Open-Smartwatch/3d-files/case-gps-0.8mm-pcb-20mm-straps/case-gps-top.stl

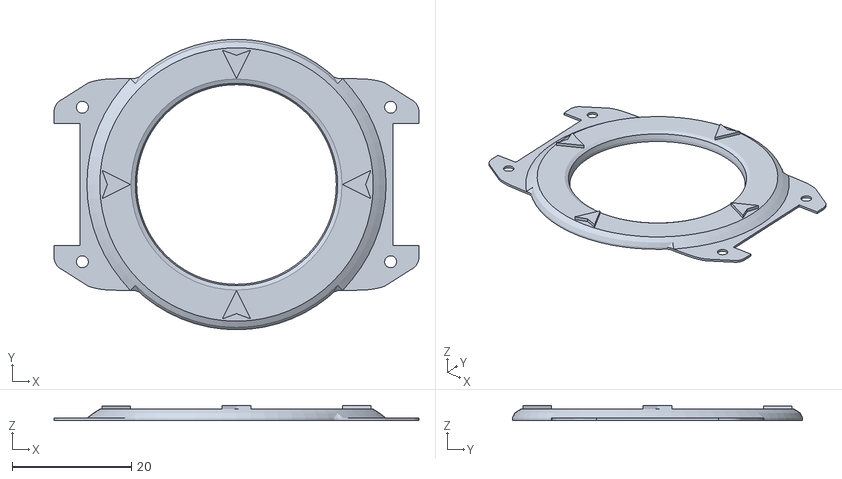
[picture p14: CAD file, 2021-03-20]
case-gps-0.8mm-pcb-20mm-straps/case-gps-top.stl
61.1 x 48.6 x 2.50
