Open-Smartwatch/3d-files/case-light-0.8mm-pcb-20mm-straps/case-light-0.8mm-pcb-20mm-straps-2-pla.stl

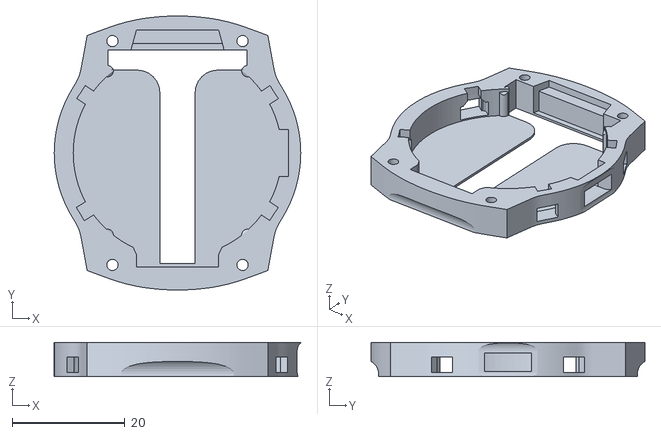
[picture p15: CAD file, 2021-04-03]
case-light-0.8mm-pcb-20mm-straps/case-light-0.8mm-pcb-20mm-straps-2-pla.stl
43.7 x 48.6 x 6.10
