Open-Smartwatch/3d-files/case-light-1.6mm-pcb-20mm-straps/case-light-1.6mm-pcb-20mm-straps-2-pla.stl

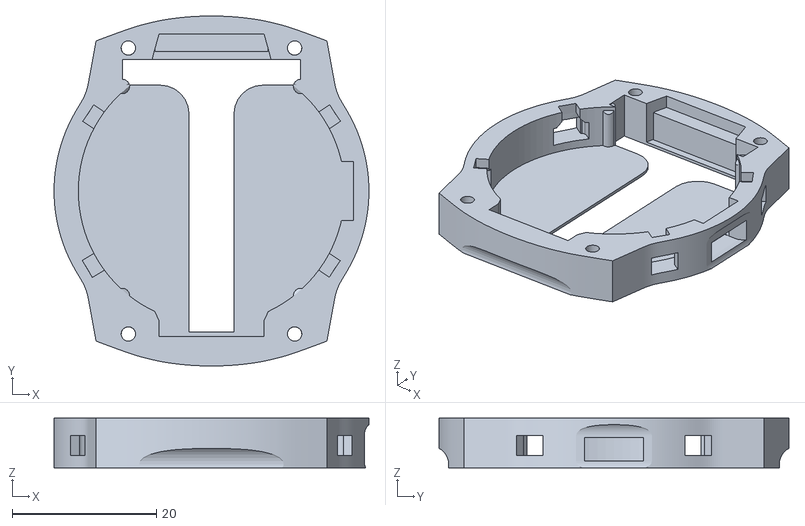
[picture p17: CAD file, 2021-04-03]
case-light-1.6mm-pcb-20mm-straps/case-light-1.6mm-pcb-20mm-straps-2-pla.stl
43.7 x 48.6 x 6.90
