Open-Smartwatch/3d-files/case-light-round-0.8mm-pcb-printed-straps/case-light-round-0.8mm-pcb-printed-straps-2-pla.stl

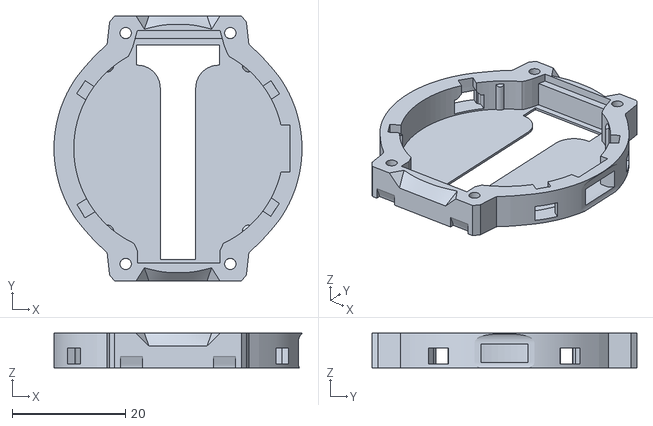
[picture p18: CAD file, 2021-03-21]
case-light-round-0.8mm-pcb-printed-straps/case-light-round-0.8mm-pcb-printed-straps-2-pla.stl
43.7 x 46.7 x 6.10
