Open-Smartwatch/3d-files/case-light-round-1.6mm-pcb-20mm-straps-coffeblock/case-bottom-light-round-1.6mm-pcb-20mm-straps-coffeblock.stl

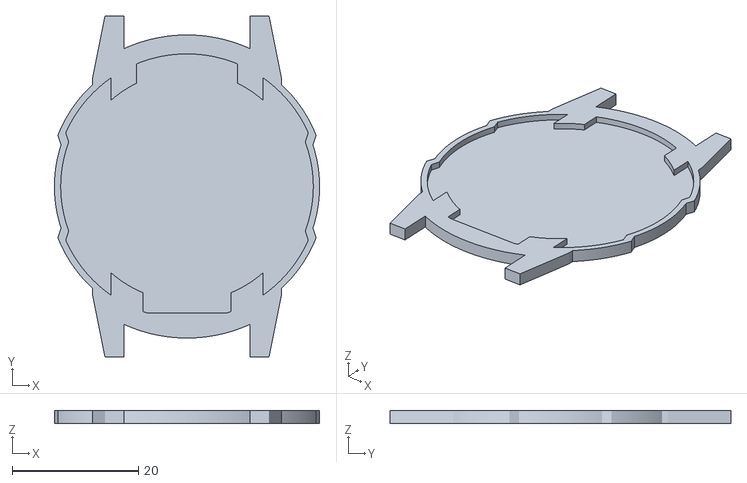
[picture p19: CAD file, 2025-01-22]
case-light-round-1.6mm-pcb-20mm-straps-coffeblock/case-bottom-light-round-1.6mm-pcb-20mm-straps-coffeblock.stl
42.0 x 54.0 x 2.00
