Open-Smartwatch/3d-files/case-light-round-1.6mm-pcb-20mm-straps-flex-buttons/case-light-round-1.6mm-case-bot.stl

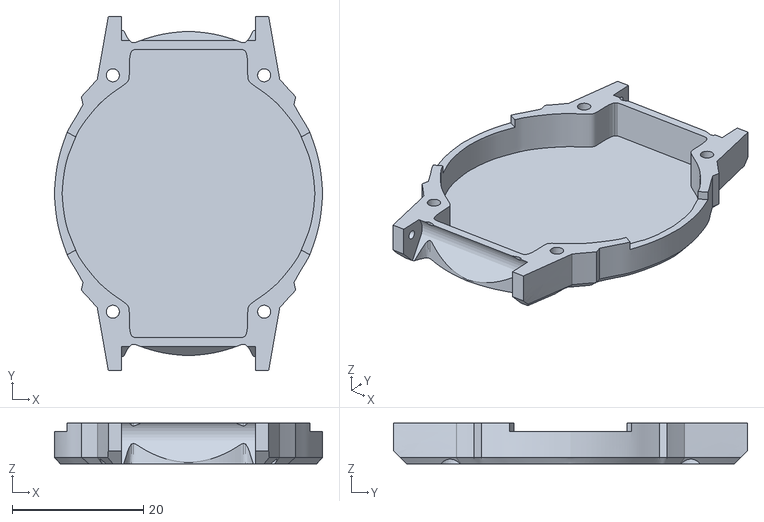
[picture p20: CAD file, 2021-04-13]
case-light-round-1.6mm-pcb-20mm-straps-flex-buttons/case-light-round-1.6mm-case-bot.stl
40.9 x 54.0 x 6.25
