Open-Smartwatch/3d-files/case-light-round-1.6mm-pcb-20mm-straps/case-light-round-1.6mm-pcb-20mm-straps-2-pla.stl

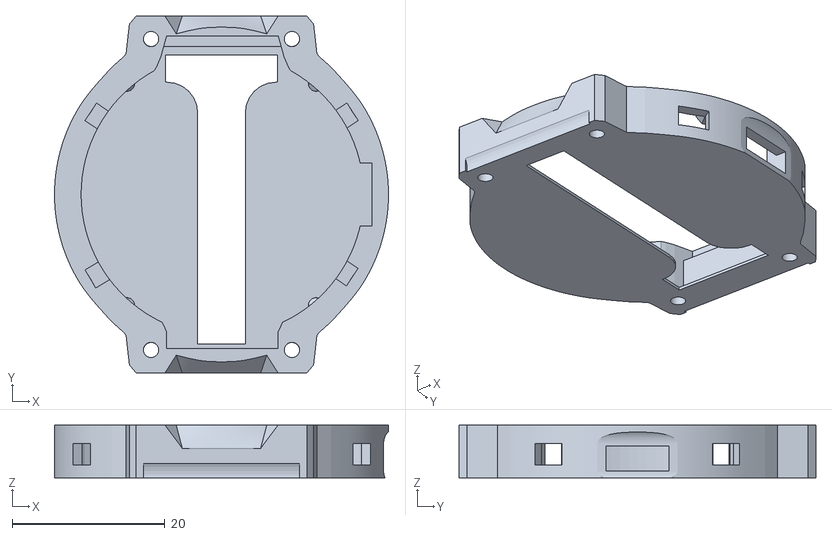
[picture p21: CAD file, 2021-04-25]
case-light-round-1.6mm-pcb-20mm-straps/case-light-round-1.6mm-pcb-20mm-straps-2-pla.stl
43.7 x 46.7 x 6.90
