Open-Smartwatch/3d-files/case-light-round-parametric/1.6mm_buttons.stl

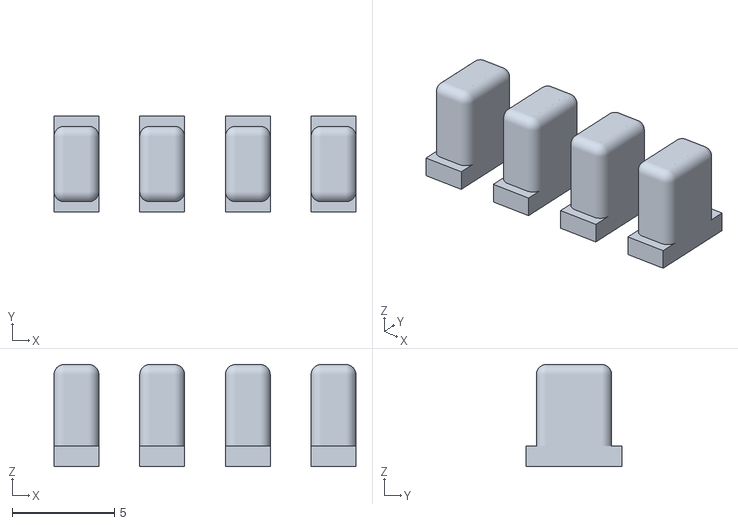
[picture p22: CAD file, 2025-10-01]
case-light-round-parametric/1.6mm_buttons.stl
14.8 x 4.70 x 5.00
