Open-Smartwatch/3d-files/case-light-thickrectangle-1.6mm-pcb-20mm-straps-lugless/LuglessOpenSmartwatch_RoundButton v1.obj

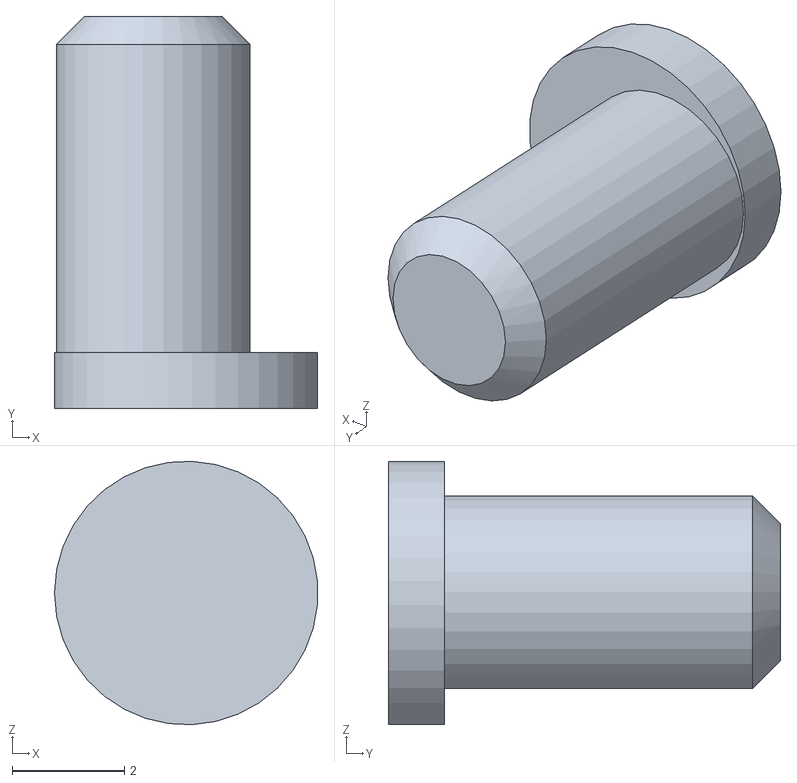
[picture p23: CAD file, 2021-05-20]
case-light-thickrectangle-1.6mm-pcb-20mm-straps-lugless/LuglessOpenSmartwatch_RoundButton v1.obj
4.69 x 7.00 x 4.70
