Open-Smartwatch/3d-files/electronic-parts-light/battery.STEP

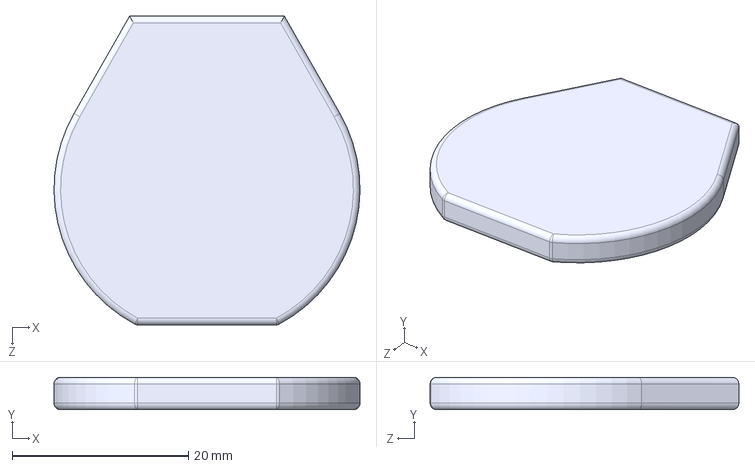
[picture p24: CAD file, 2021-05-20]
electronic-parts-light/battery.STEP
34.7 x 3.68 x 35.0 mm
