Open-Smartwatch/3d-files/ultrathin-case-light-1.6mm-pcb-20mm-straps/CaseTop.stl

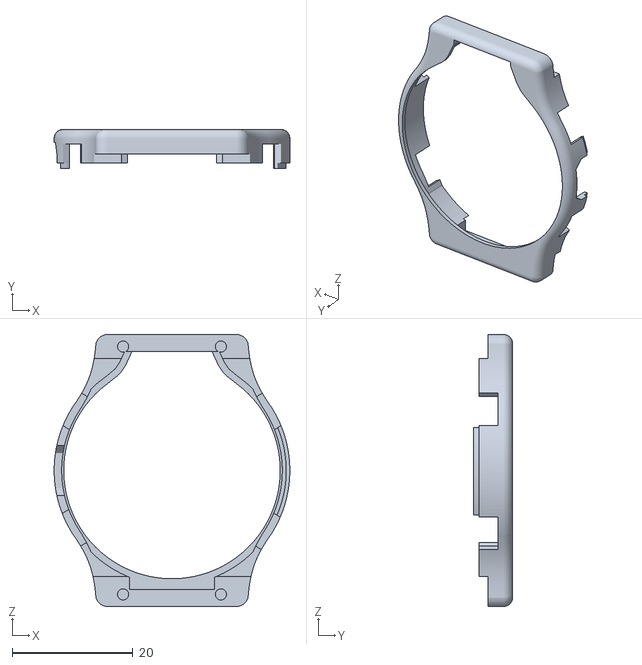
[picture p26: CAD file, 2025-10-01]
ultrathin-case-light-1.6mm-pcb-20mm-straps/CaseTop.stl
39.0 x 6.50 x 45.0
