Open-Smartwatch/3d-files/wrist-strap-linked/wrist-strap-linked-2-pla.stl

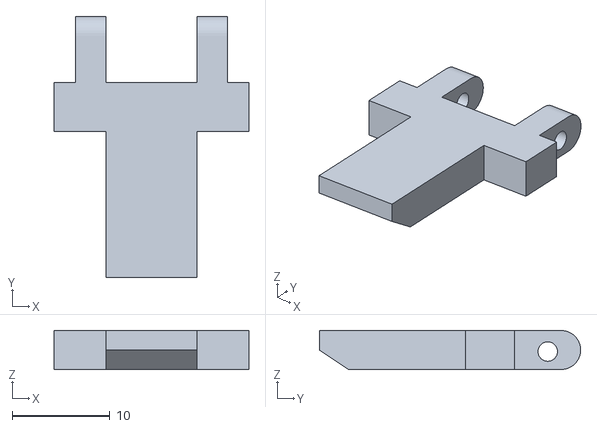
[picture p27: CAD file, 2021-03-20]
wrist-strap-linked/wrist-strap-linked-2-pla.stl
20.0 x 26.8 x 4.00
