Open-Smartwatch/3d-files/wrist-strap-tpu/wrist-strap-flex-1-tpu.stl

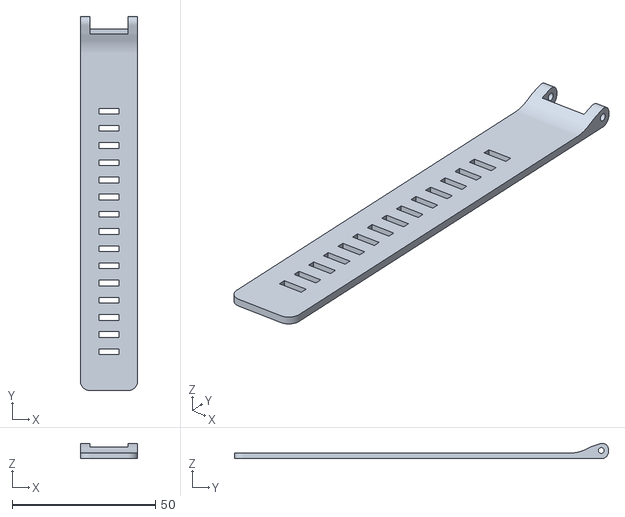
[picture p28: CAD file, 2021-03-20]
wrist-strap-tpu/wrist-strap-flex-1-tpu.stl
20.0 x 130.6 x 5.33
