Open-Smartwatch/3d-files/case-gps-0.8mm-pcb-20mm-straps/case-gps-mid.stl

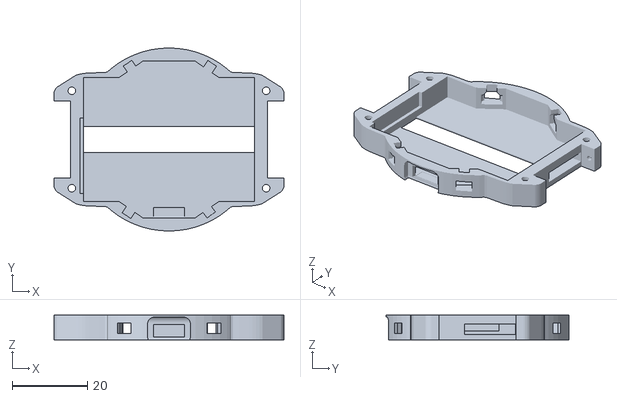
[picture p29: CAD file, 2021-03-20]
case-gps-0.8mm-pcb-20mm-straps/case-gps-mid.stl
61.1 x 48.6 x 6.60
