Open-Smartwatch/3d-files/case-light-1.6mm-pcb-printed-straps/case-light-1.6mm-pcb-printed-straps-3-pla.stl

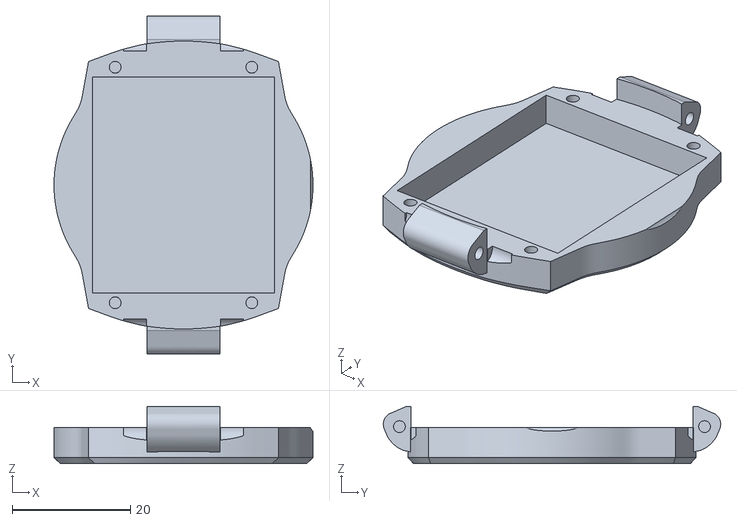
[picture p30: CAD file, 2021-03-20]
case-light-1.6mm-pcb-printed-straps/case-light-1.6mm-pcb-printed-straps-3-pla.stl
43.7 x 57.0 x 9.67
