Open-Smartwatch/3d-files/case-light-round-1.6mm-pcb-20mm-straps-flex-buttons/case-light-round-1.6mm-case-top-cnc.stl

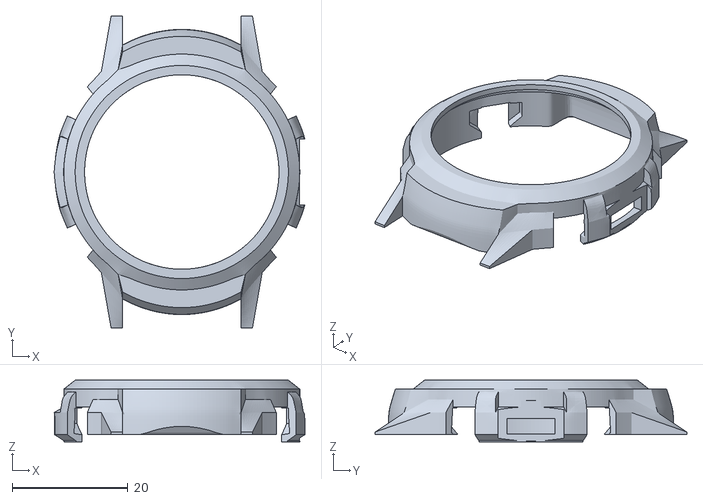
[picture p32: CAD file, 2021-04-13]
case-light-round-1.6mm-pcb-20mm-straps-flex-buttons/case-light-round-1.6mm-case-top-cnc.stl
43.4 x 54.0 x 10.7
