Open-Smartwatch/3d-files/case-light-round-1.6mm-pcb-20mm-straps/case-light-round-1.6mm-pcb-20mm-straps-1-pla.stl

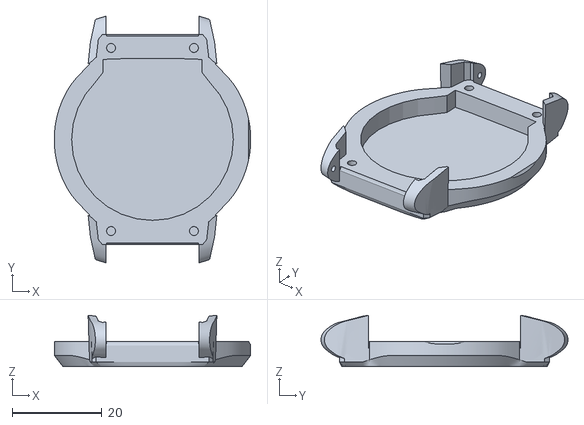
[picture p33: CAD file, 2021-04-23]
case-light-round-1.6mm-pcb-20mm-straps/case-light-round-1.6mm-pcb-20mm-straps-1-pla.stl
43.7 x 55.0 x 11.4
