Open-Smartwatch/3d-files/case-light-round-1.6mm-pcb-printed-straps/case-light-round-1.6mm-pcb-printed-straps-3-pla.stl

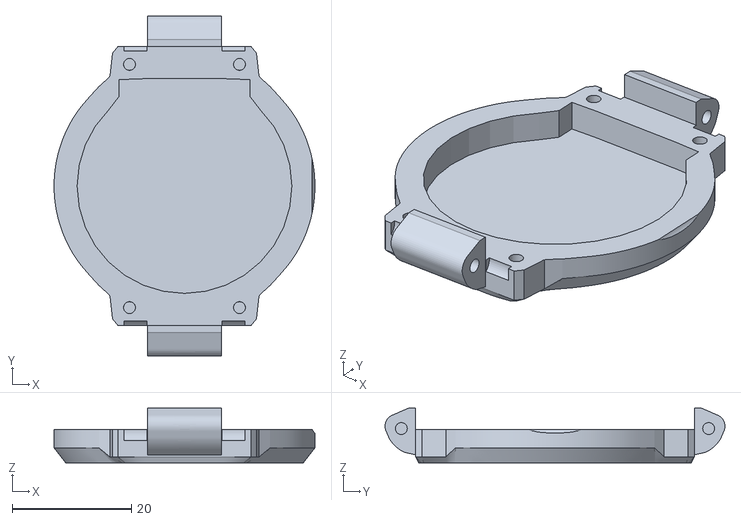
[picture p34: CAD file, 2021-03-20]
case-light-round-1.6mm-pcb-printed-straps/case-light-round-1.6mm-pcb-printed-straps-3-pla.stl
43.7 x 57.0 x 9.17
