Open-Smartwatch/3d-files/case-light-round-parametric/1.6mm_base.stl

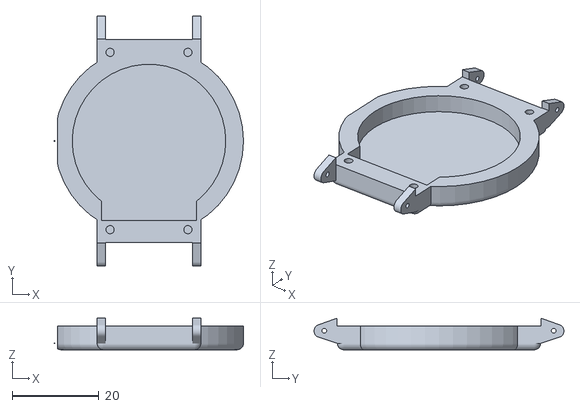
[picture p35: CAD file, 2025-10-01]
case-light-round-parametric/1.6mm_base.stl
43.7 x 57.8 x 7.30
