Open-Smartwatch/3d-files/case-light-thickrectangle-1.6mm-pcb-20mm-straps-lugless/LuglessOpenSmartwatch_Upper.stl

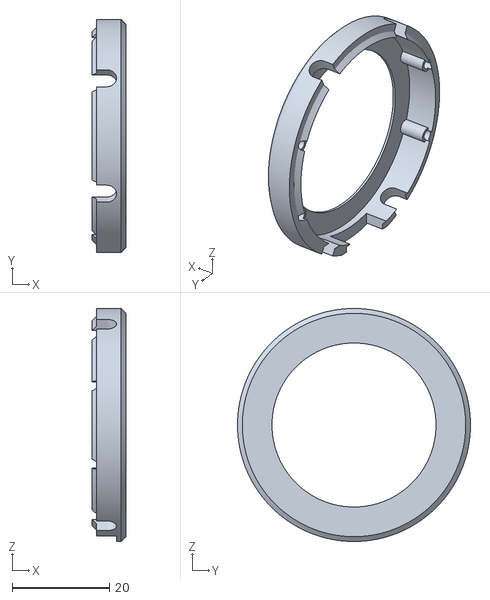
[picture p36: CAD file, 2021-05-20]
case-light-thickrectangle-1.6mm-pcb-20mm-straps-lugless/LuglessOpenSmartwatch_Upper.stl
6.97 x 48.0 x 48.0
