Open-Smartwatch/3d-files/ultrathin-case-light-1.6mm-pcb-20mm-straps/CaseBottom.stl

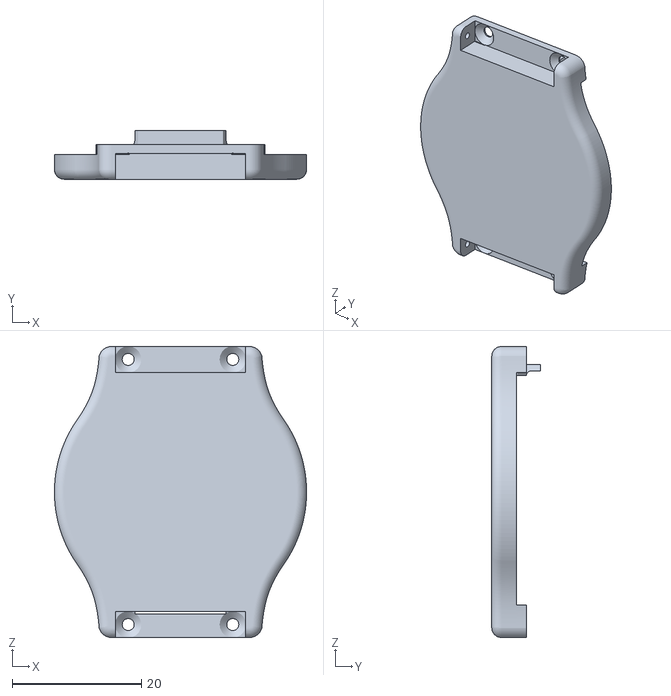
[picture p37: CAD file, 2025-10-01]
ultrathin-case-light-1.6mm-pcb-20mm-straps/CaseBottom.stl
39.0 x 7.50 x 45.0
