Open-Smartwatch/3d-files/wrist-strap-linked/wrist-strap-linked-1-pla.stl

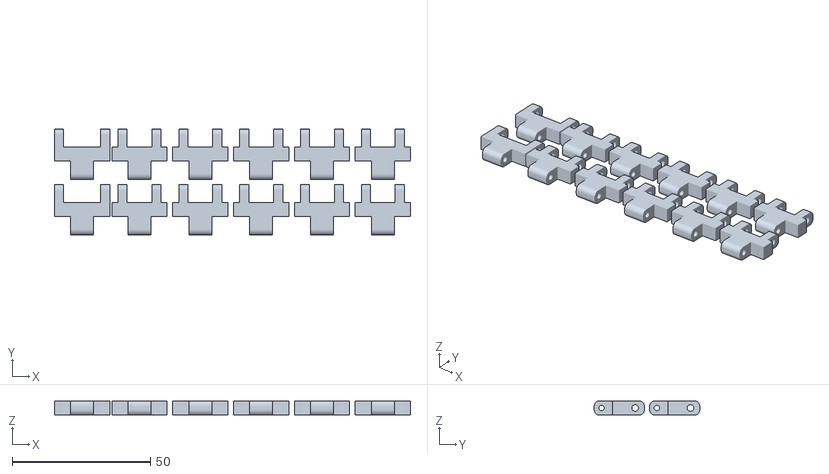
[picture p38: CAD file, 2021-03-20]
wrist-strap-linked/wrist-strap-linked-1-pla.stl
128.7 x 38.2 x 5.20
