Open-Smartwatch/3d-files/wrist-strap-tpu/wrist-strap-flex-2-tpu.stl

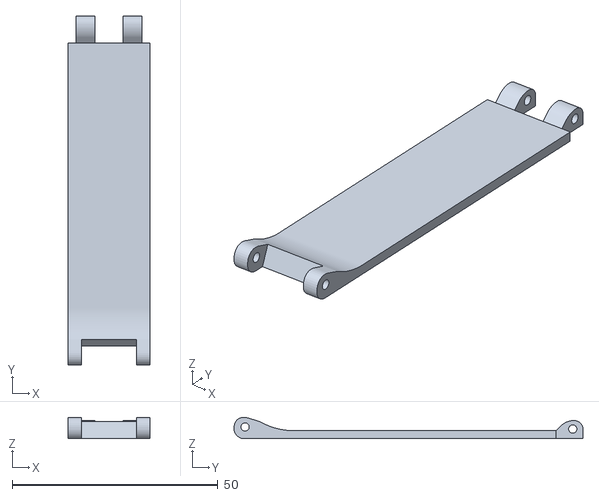
[picture p39: CAD file, 2021-03-20]
wrist-strap-tpu/wrist-strap-flex-2-tpu.stl
20.0 x 84.7 x 5.20
