Open-Smartwatch/3d-files/case-light-round-1.6mm-pcb-20mm-straps-flex-buttons/buttons.stl

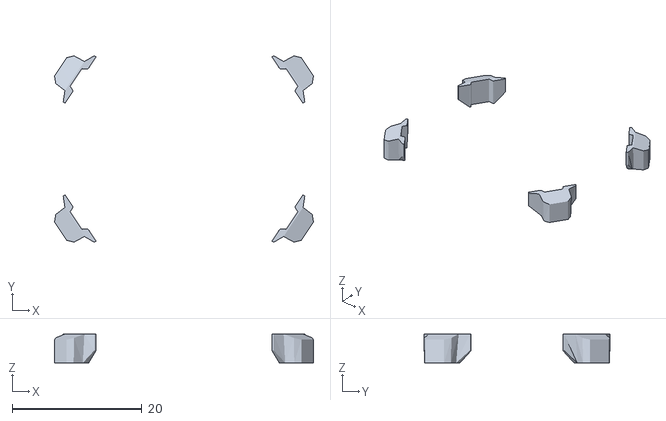
[picture p40: CAD file, 2021-04-05]
case-light-round-1.6mm-pcb-20mm-straps-flex-buttons/buttons.stl
39.9 x 28.7 x 4.47
