Open-Smartwatch/3d-files/case-light-round-parametric/1.6mm_strap.stl

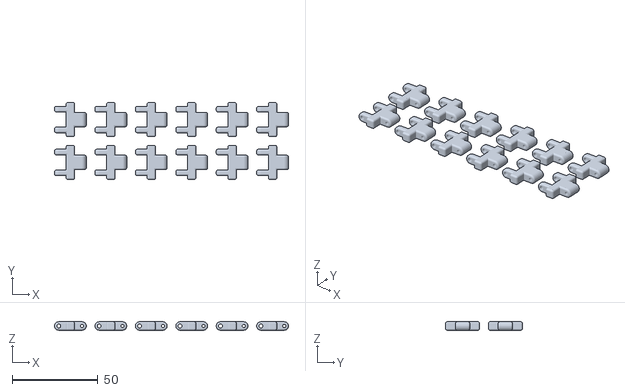
[picture p41: CAD file, 2025-10-01]
case-light-round-parametric/1.6mm_strap.stl
136.6 x 45.0 x 5.00
