Open-Smartwatch/3d-files/sleek-case-light-round-1.6mm-pcb-20mm-straps/sleek-case-light-round-1.6mm-pcb-20mm-straps-step-files/button.STEP

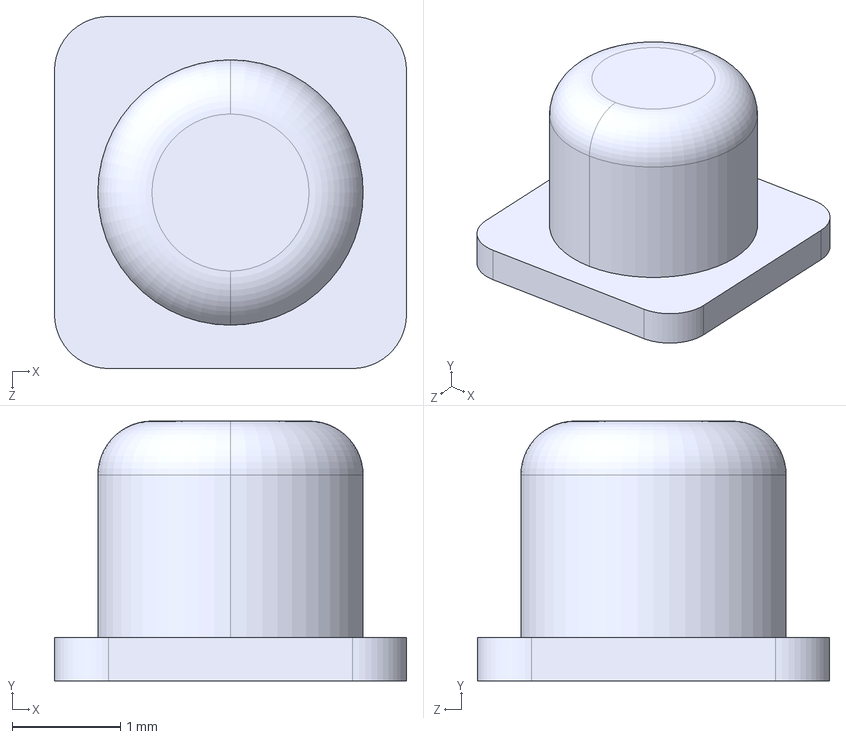
[picture p42: CAD file, 2021-05-20]
sleek-case-light-round-1.6mm-pcb-20mm-straps/sleek-case-light-round-1.6mm-pcb-20mm-straps-step-files/button.STEP
3.25 x 2.40 x 3.25 mm
