Open-Smartwatch/3d-files/ultrathin-case-light-1.6mm-pcb-20mm-straps/Case.step

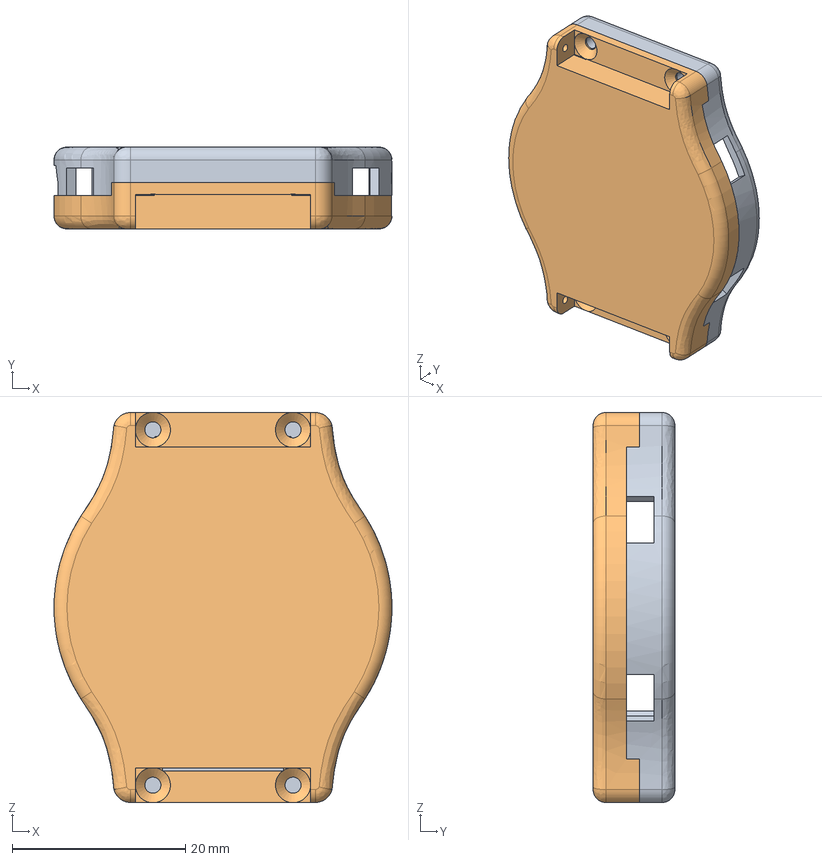
[picture p43: CAD file, 2025-10-01]
ultrathin-case-light-1.6mm-pcb-20mm-straps/Case.step
39.0 x 9.45 x 45.0 mm
