Open-Smartwatch/3d-files/wrist-strap-tpu/wrist-strap-flex-4-pla.stl

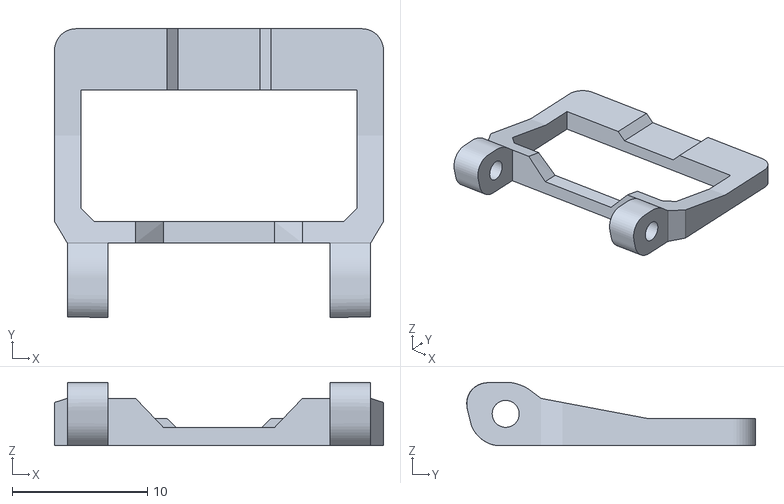
[picture p44: CAD file, 2021-03-20]
wrist-strap-tpu/wrist-strap-flex-4-pla.stl
24.3 x 21.4 x 4.69
