Open-Smartwatch/3d-files/case-light-round-1.6mm-pcb-20mm-straps-flex-buttons/case-light-round-1.6mm-flex-top.stl

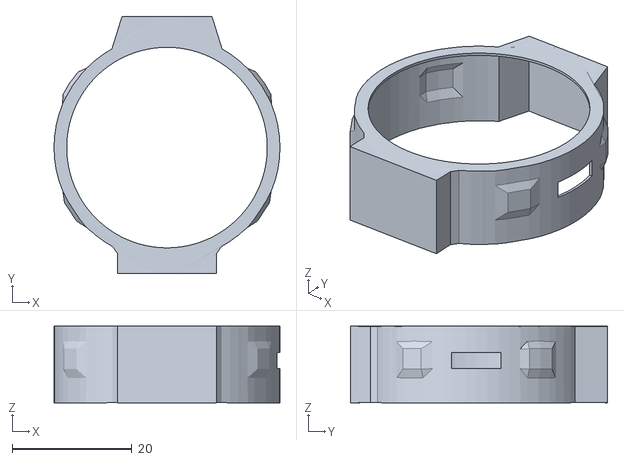
[picture p45: CAD file, 2021-04-03]
case-light-round-1.6mm-pcb-20mm-straps-flex-buttons/case-light-round-1.6mm-flex-top.stl
37.8 x 43.0 x 12.8
