Open-Smartwatch/3d-files/case-light-round-parametric/1.6mm_base_printed_strap.stl

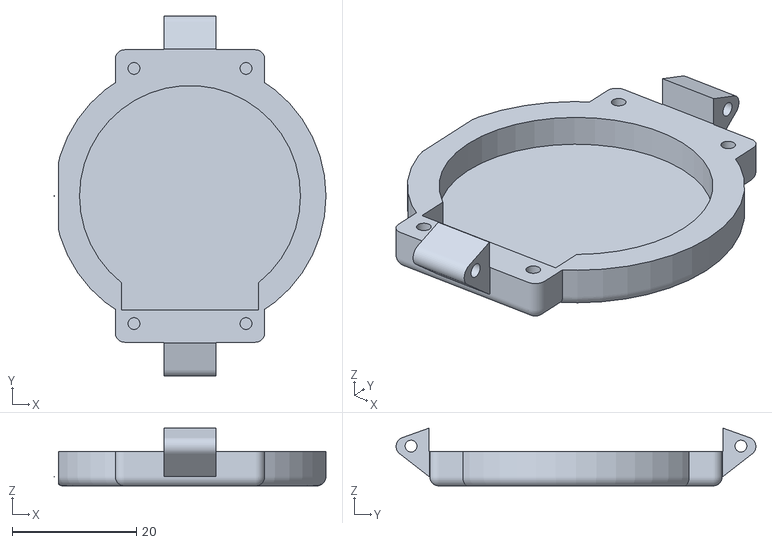
[picture p46: CAD file, 2025-10-01]
case-light-round-parametric/1.6mm_base_printed_strap.stl
43.7 x 57.8 x 9.30
