Open-Smartwatch/3d-files/case-light-thickrectangle-1.6mm-pcb-20mm-straps-lugless/LuglessOpenSmartwatch_CompartmentBuffer.stl

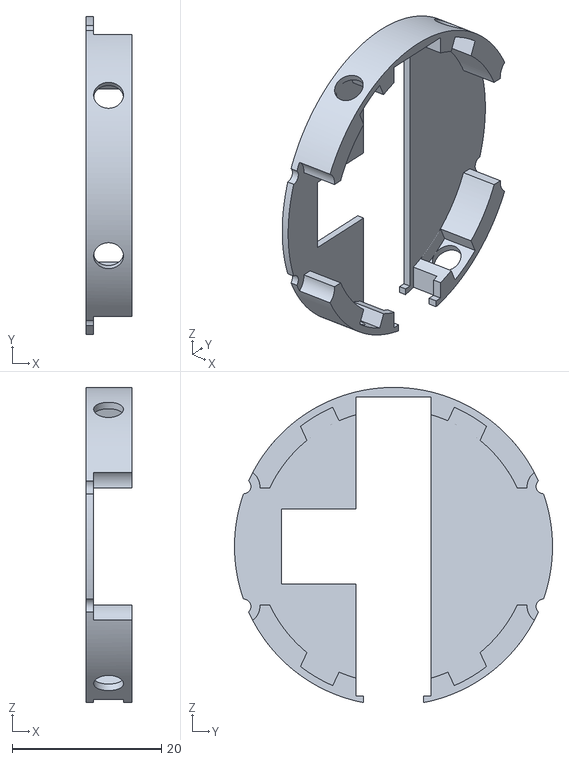
[picture p47: CAD file, 2021-05-20]
case-light-thickrectangle-1.6mm-pcb-20mm-straps-lugless/LuglessOpenSmartwatch_CompartmentBuffer.stl
6.17 x 42.6 x 42.2
