Open-Smartwatch/3d-files/sleek-case-light-round-1.6mm-pcb-20mm-straps/sleek-case-light-round-1.6mm-pcb-20mm-straps-step-files/spacer.STEP

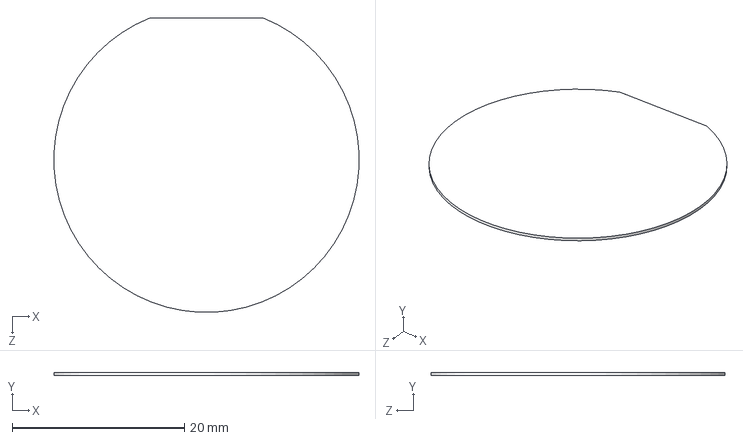
[picture p48: CAD file, 2021-05-20]
sleek-case-light-round-1.6mm-pcb-20mm-straps/sleek-case-light-round-1.6mm-pcb-20mm-straps-step-files/spacer.STEP
35.5 x 0.36 x 34.2 mm
