Open-Smartwatch/3d-files/wrist-strap-tpu/wrist-strap-flex-5-pla.stl

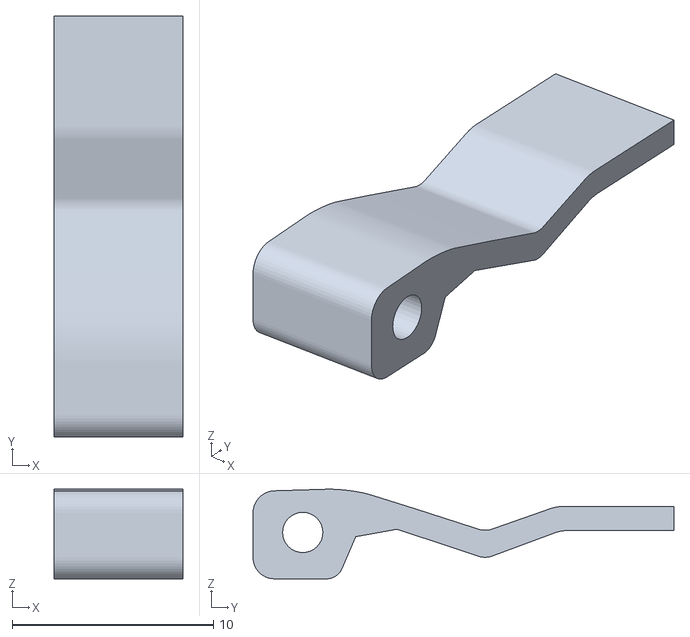
[picture p49: CAD file, 2021-03-20]
wrist-strap-tpu/wrist-strap-flex-5-pla.stl
6.40 x 20.9 x 4.45
