Open-Smartwatch/3d-files/case-light-round-1.6mm-pcb-20mm-straps-flex-buttons/case-light-round-1.6mm-flex-bot.stl

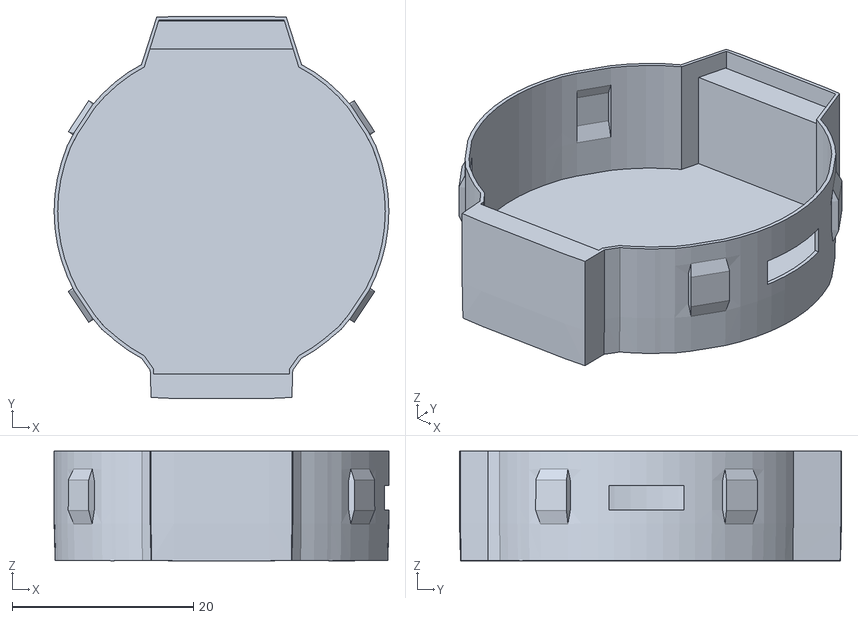
[picture p50: CAD file, 2021-04-03]
case-light-round-1.6mm-pcb-20mm-straps-flex-buttons/case-light-round-1.6mm-flex-bot.stl
37.0 x 42.2 x 12.1
