Open-Smartwatch/3d-files/case-light-round-parametric/1.6mm_mid.stl

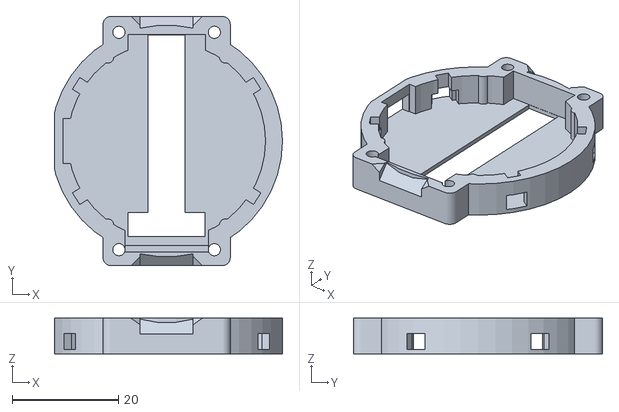
[picture p51: CAD file, 2025-10-01]
case-light-round-parametric/1.6mm_mid.stl
43.0 x 47.0 x 6.70
