Open-Smartwatch/3d-files/sleek-case-light-round-1.6mm-pcb-20mm-straps/sleek-case-light-round-1.6mm-pcb-20mm-straps-step-files/bottom.STEP

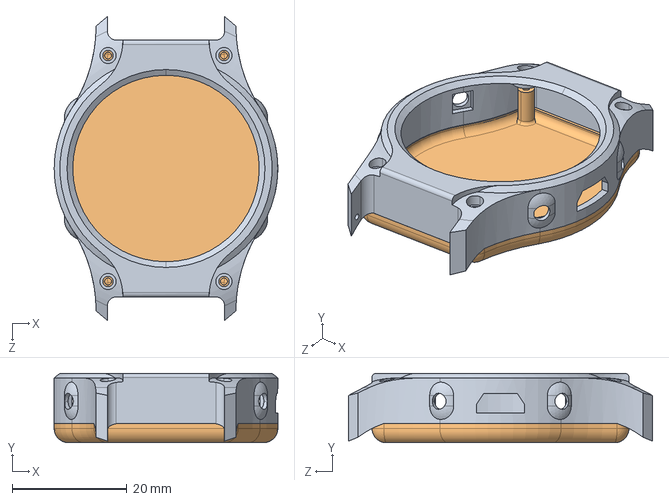
[picture p53: CAD file, 2021-05-20]
sleek-case-light-round-1.6mm-pcb-20mm-straps/sleek-case-light-round-1.6mm-pcb-20mm-straps-step-files/bottom.STEP
39.0 x 12.1 x 53.0 mm
